thvanarkel/SleepyLight/Software/sleepy-config/src/images/help02.png

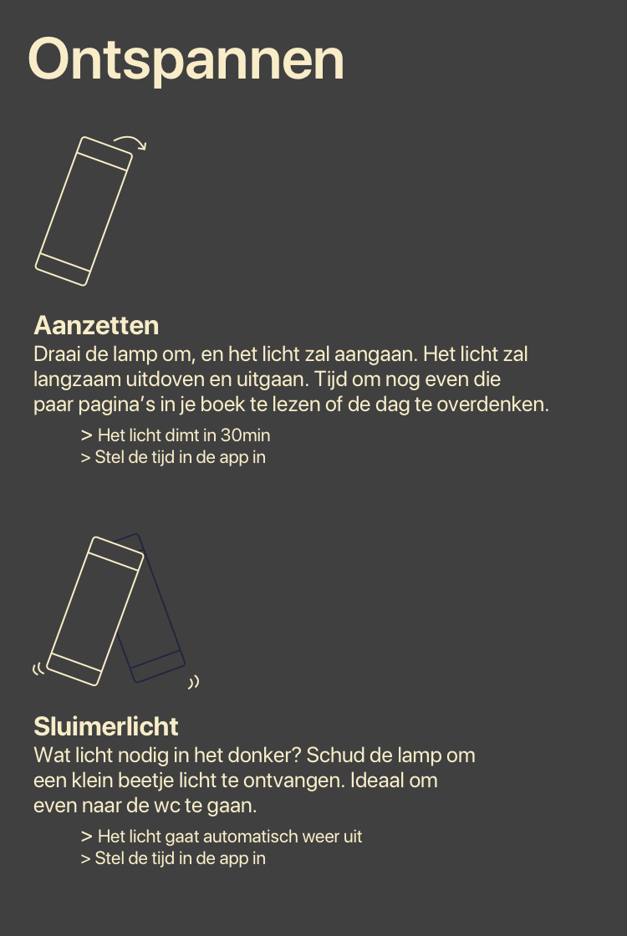
Software/sleepy-config/src/images/help02.png
