thvanarkel/SleepyLight/Software/sleepy-config/src/images/lamp.png

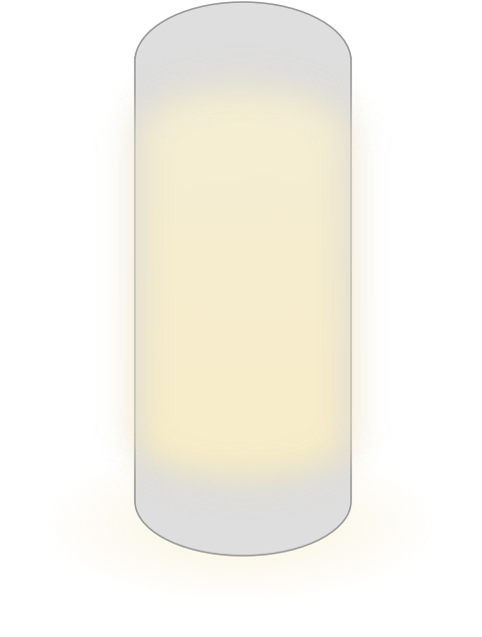
Software/sleepy-config/src/images/lamp.png
